maxistar/corney/body/dongle/dongle_breadboard_bottom.scad

use <dongle_breadboard.scad>

bottomShell();
