maxistar/corney/body/dongle/dongle_breadboard_button.scad

use <dongle_breadboard.scad>

rotate([0, 180, 0]) {
  button();
}
