maxistar/corney/body/dongle/dongle_breadboard_upper.scad

use <dongle_breadboard.scad>

rotate([180, 0, 0]) {
upperShell();
}
