maxistar/corney/body/corne_shape_with_stands.scad

include <corne_body_models.scad>;


// corne shape with stands
body_solid();
