maxistar/corney/body/Choc_Version/face_panel.scad

use <body_thin.scad>

panel();
