maxistar/corney/body/Choc_Version/reset_button_right.scad

use <reset_button.scad>

$fn = 150;


module resetButtonSmall() {
  resetButton(7);
}

resetButtonSmall();
