maxistar/corney/body/Choc_Version/right_touchpad_cover.scad

use <board_cover_touchpad.scad>

// Printable cover for the canonical right-hand Cirque half.
module rightTouchpadCover() {
  cover_touchpad();
}

rightTouchpadCover();
