maxistar/corney/body/MX_Version/panel.scad

difference() {

  linear_extrude(1.5) {
    import("plate_outline.svg");
  }

  translate([0, 0, -5])
    linear_extrude(10) {
      import("buttons.svg");
    }

  translate([0, 0, -5])
    linear_extrude(10) {
      import("holes.svg");
    }
}
